dmcke5/SimPedals/Printed Components/Limit Stop Tube x6.STL

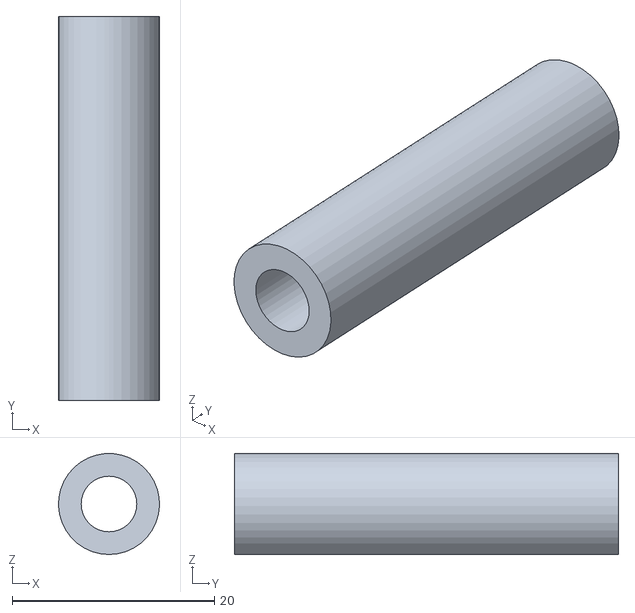
[picture p16: CAD file, 2025-04-28]
Printed Components/Limit Stop Tube x6.STL
9.99 x 38.0 x 10.0
