dmcke5/SimPedals/Metal Components/Steel Parts/2mm Foot Plate x1.STEP

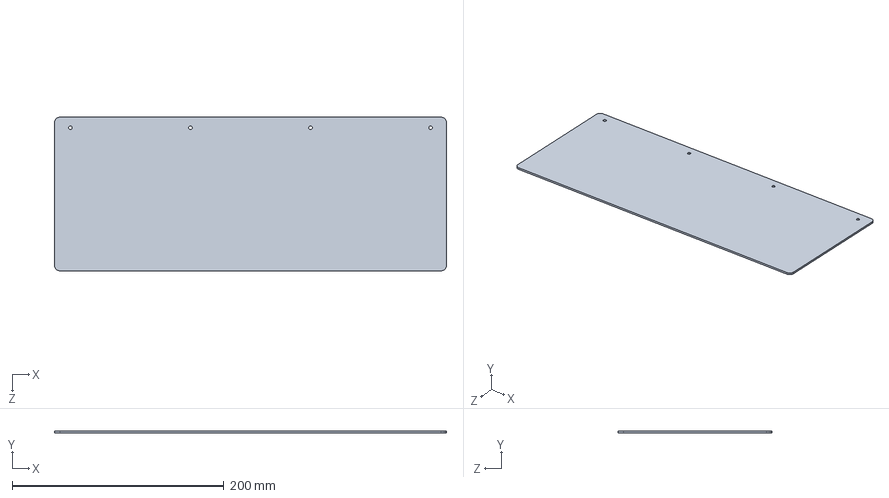
[picture p17: CAD file, 2025-04-28]
Metal Components/Steel Parts/2mm Foot Plate x1.STEP
370.0 x 2.00 x 145.0 mm
