dmcke5/SimPedals/Printed Components/Foot Rest Support (Mirror pair).STL

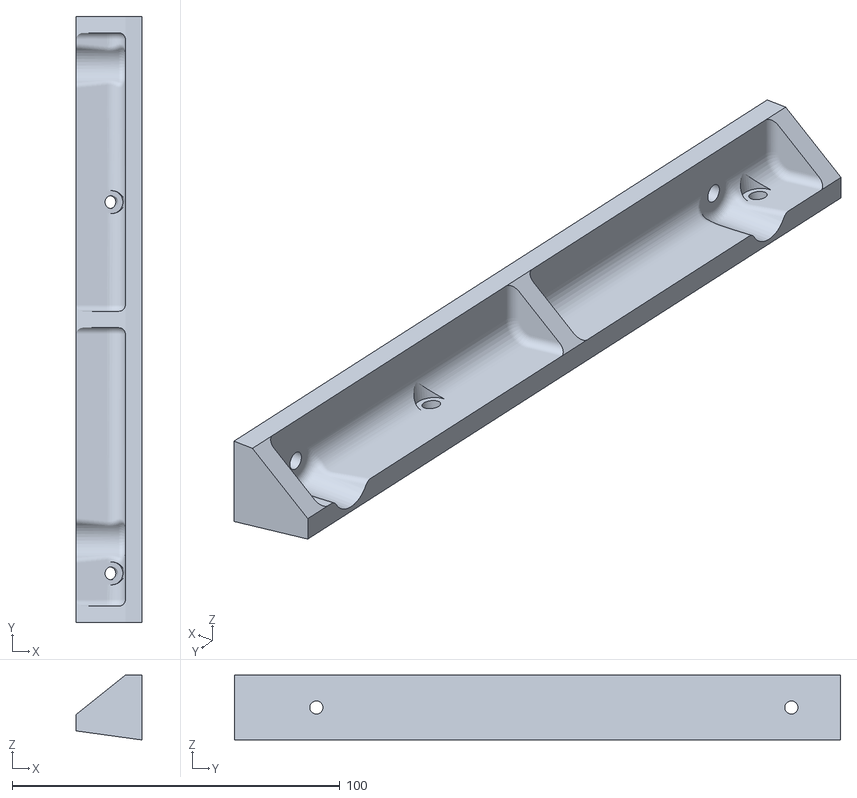
[picture p18: CAD file, 2025-04-28]
Printed Components/Foot Rest Support (Mirror pair).STL
20.0 x 185.0 x 19.8
