dmcke5/SimPedals/Metal Components/Steel Parts/3mm Load Cell Bracket x1.DXF

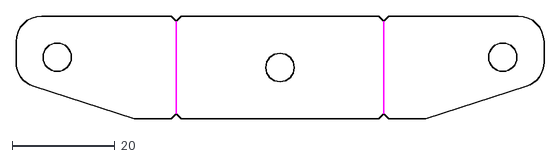
[picture p19: CAD file, 2025-04-28]
Metal Components/Steel Parts/3mm Load Cell Bracket x1.DXF
102.5 x 20.0
