dmcke5/SimPedals/Printed Components/Pedal Bearing Crush Tube x3.STL

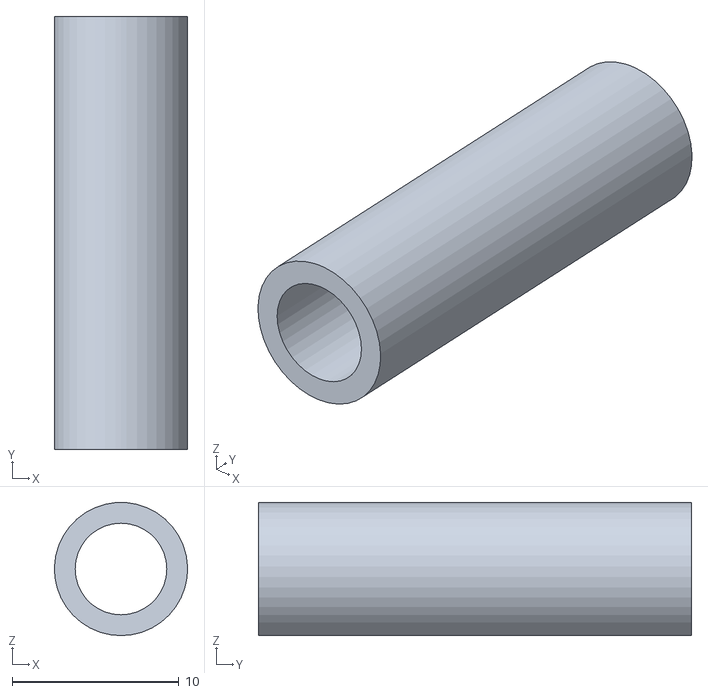
[picture p20: CAD file, 2025-04-28]
Printed Components/Pedal Bearing Crush Tube x3.STL
7.99 x 26.0 x 8.00
