dmcke5/SimPedals/Printed Components/Brake pedal form (Don't print if using printed pedals).STL

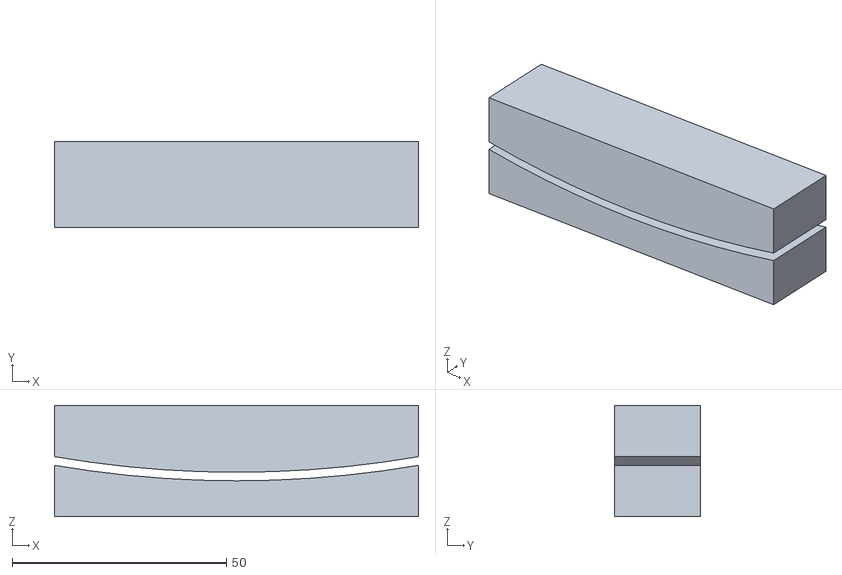
[picture p21: CAD file, 2025-04-28]
Printed Components/Brake pedal form (Don't print if using printed pedals).STL
85.0 x 20.0 x 26.0
