dmcke5/SimPedals/Printed Components/TPE Brake Bushing.STL

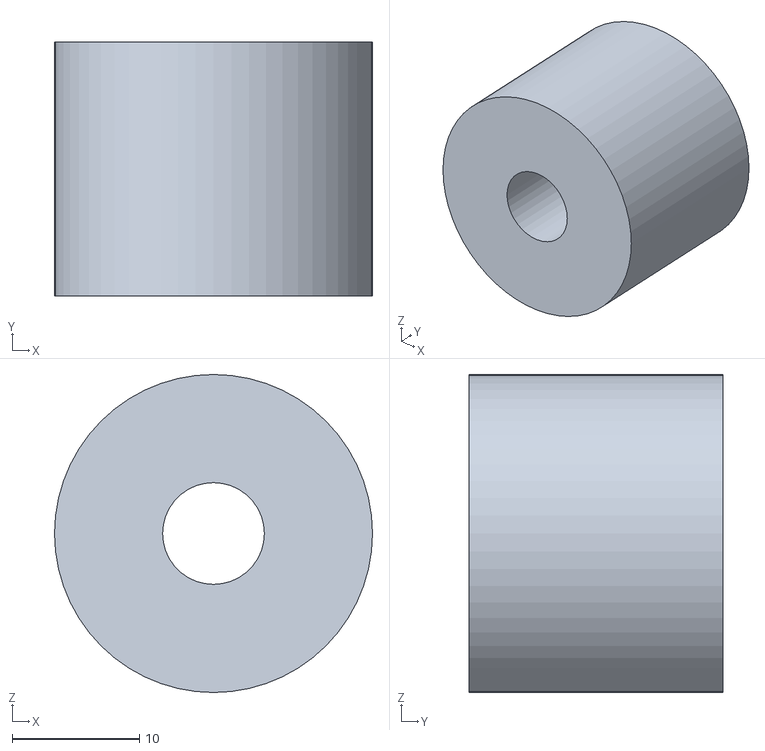
[picture p22: CAD file, 2025-04-28]
Printed Components/TPE Brake Bushing.STL
25.0 x 20.0 x 25.0
