dmcke5/SimPedals/Printed Components/Spring Seat x6.STL

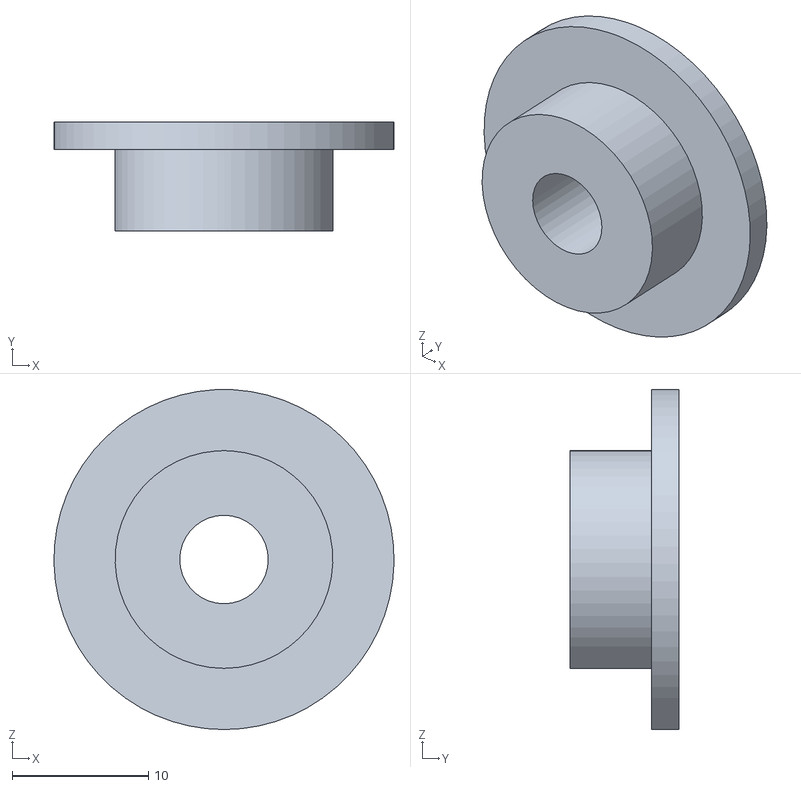
[picture p23: CAD file, 2025-04-28]
Printed Components/Spring Seat x6.STL
25.0 x 8.00 x 25.0
