dmcke5/SimPedals/Printed Components/Hall Effect Mount x2.STL

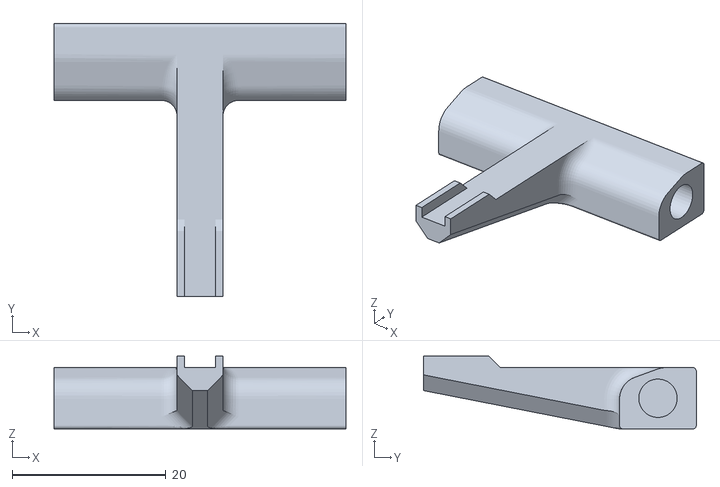
[picture p24: CAD file, 2025-04-28]
Printed Components/Hall Effect Mount x2.STL
38.0 x 35.5 x 9.50
