dmcke5/SimPedals/Printed Components/Slide Bush x3.STL

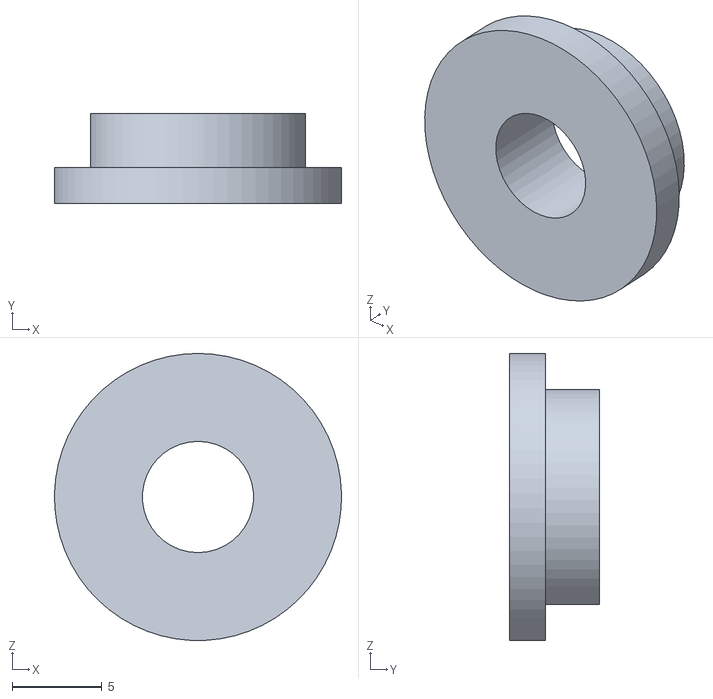
[picture p25: CAD file, 2025-04-28]
Printed Components/Slide Bush x3.STL
16.0 x 5.00 x 16.0
