dmcke5/SimPedals/Printed Components/Clevis Spacer x6.STL

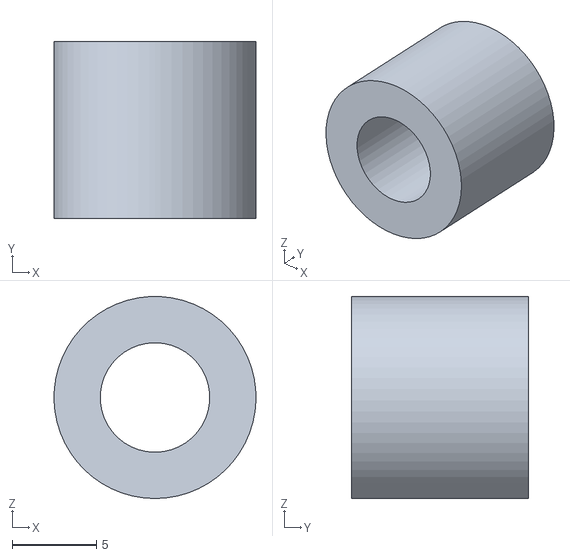
[picture p26: CAD file, 2025-04-28]
Printed Components/Clevis Spacer x6.STL
12.0 x 10.5 x 12.0
